adamforbes92/OpenHaldex-T4/Code/openhaldex_vers.h

/*
Section dedicated ENTIRELY for version tracking(!)

V1.09 - Initial release, poor version tracking until now.  Basic code + Gen1 major support
V1.10 - dialled in Gen2; working on the bench.  Has change in range (0-255?), mostly controlled by Bremse
      - added flashing red LED for no CANBUS comms.  Added standalone but allow diagnostic data through - so Haldex can be diagnosed with VCDS etc
V1.11 - added in Gen4 - standalone confirmed and copied data to 'OEM'.  To be confirmed if working, but standalone does so would just need frames 'added' if req.
*/
